Ryanemzed/Self-Serve-Case/case-files/Self Serve - Mini/5 - Bottom Panel/5 - McM.dxf

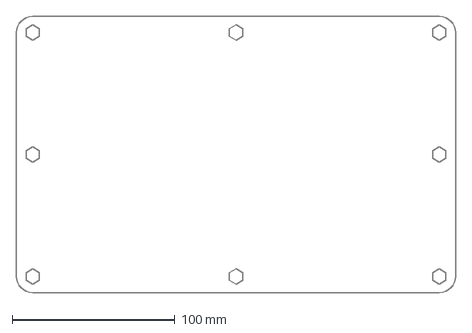
[picture p16: CAD file, 2024-07-01]
case-files/Self Serve - Mini/5 - Bottom Panel/5 - McM.dxf
270.0 x 170.0 mm
