Ryanemzed/Self-Serve-Case/case-files/Self Serve - Standard/1 - Button Panel/1 - UXC.dxf

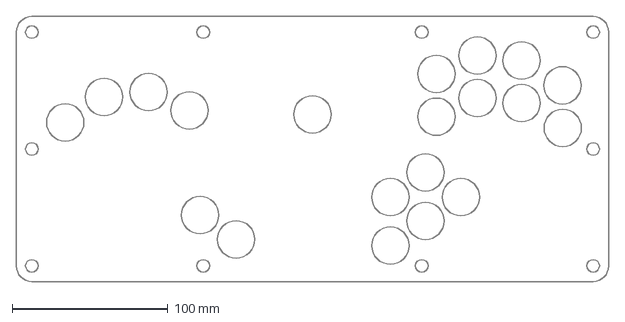
[picture p17: CAD file, 2024-07-01]
case-files/Self Serve - Standard/1 - Button Panel/1 - UXC.dxf
380.0 x 170.0 mm
