Ryanemzed/Self-Serve-Case/case-files/Self Serve - Standard/2 - Under Panel/2 - McM.dxf

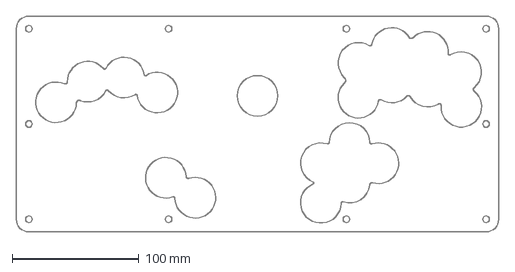
[picture p18: CAD file, 2024-07-01]
case-files/Self Serve - Standard/2 - Under Panel/2 - McM.dxf
380.0 x 170.0 mm
