Ryanemzed/Self-Serve-Case/case-files/Self Serve - Standard/5 - Bottom Panel/5 - UXC.dxf

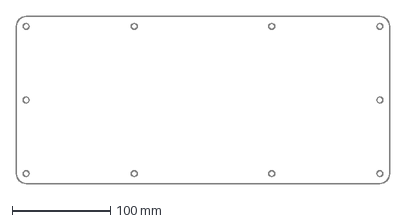
[picture p20: CAD file, 2024-07-01]
case-files/Self Serve - Standard/5 - Bottom Panel/5 - UXC.dxf
380.0 x 170.0 mm
