Ryanemzed/Self-Serve-Case/case-files/Self Serve - Mini/3 - USBC/3 - UXC - HT.dxf

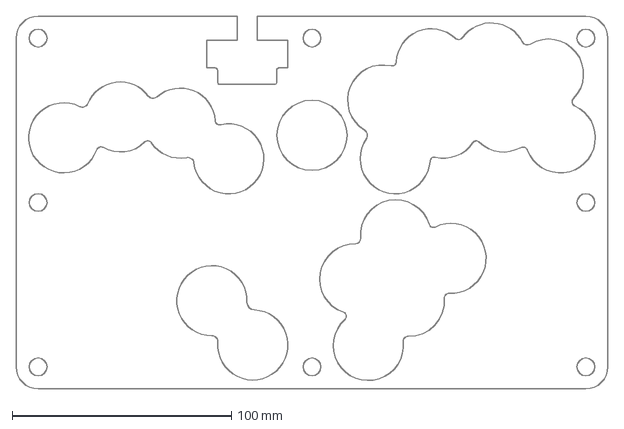
[picture p21: CAD file, 2024-07-01]
case-files/Self Serve - Mini/3 - USBC/3 - UXC - HT.dxf
270.0 x 170.0 mm
