Ryanemzed/Self-Serve-Case/case-files/Self Serve - Standard/3 - USBC/3 - UXC - HT.dxf

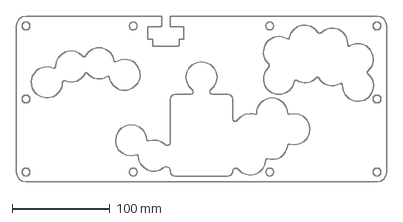
[picture p23: CAD file, 2024-07-01]
case-files/Self Serve - Standard/3 - USBC/3 - UXC - HT.dxf
380.0 x 170.0 mm
