Ryanemzed/Self-Serve-Case/case-files/Self Serve - Mini/3 - USBC/3 - McM - HT.dxf

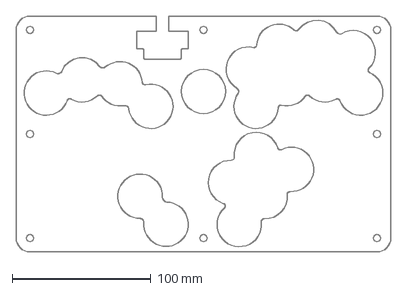
[picture p25: CAD file, 2024-07-01]
case-files/Self Serve - Mini/3 - USBC/3 - McM - HT.dxf
270.0 x 170.0 mm
