Ryanemzed/Self-Serve-Case/case-files/Self Serve - Standard/4 - Wiring Panel/4 - McM - HT - Hollow.dxf

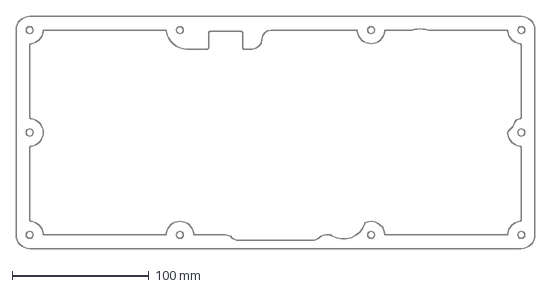
[picture p28: CAD file, 2024-07-01]
case-files/Self Serve - Standard/4 - Wiring Panel/4 - McM - HT - Hollow.dxf
380.0 x 170.0 mm
