Ryanemzed/Self-Serve-Case/case-files/Self Serve - Mini/4 - Wiring Panel/4 - McM - AE - Hollow.dxf

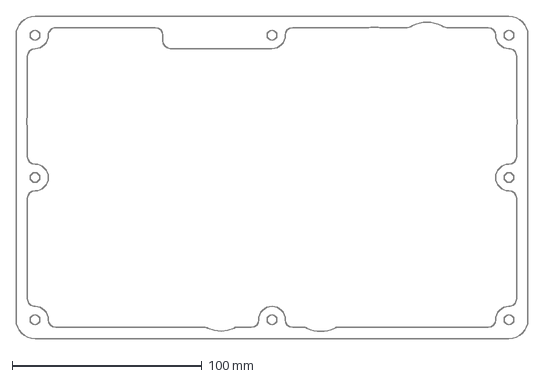
[picture p32: CAD file, 2024-07-01]
case-files/Self Serve - Mini/4 - Wiring Panel/4 - McM - AE - Hollow.dxf
270.0 x 170.0 mm
